finnhittson-creator/pogostick/pogostick/pogostick.kicad_sch

## KiCad design pogostick/pogostick.kicad_sch (2026-09-18)

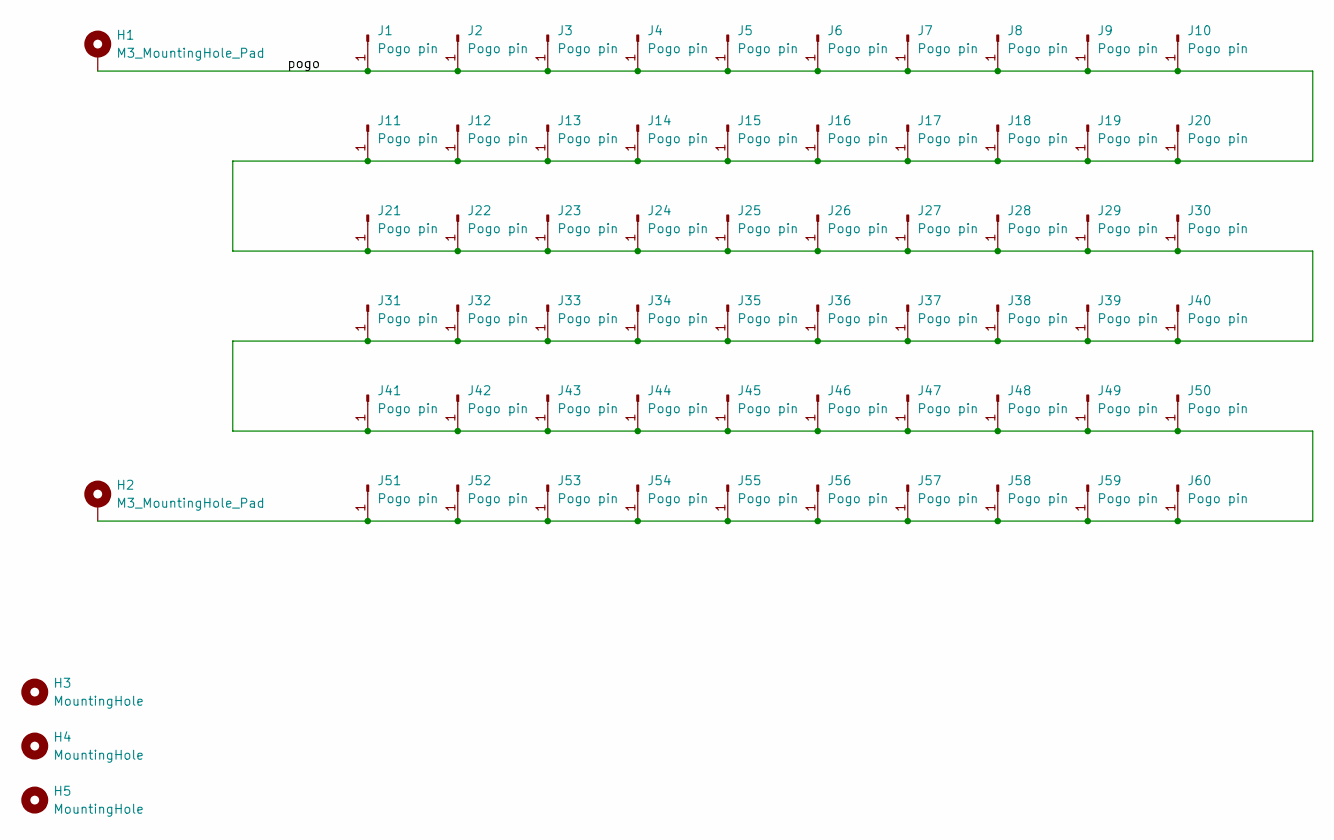
[picture p8: schematic pogostick.kicad_sch]

Parts:
H1, H2: M3_MountingHole_Pad; MountingHole_3.2mm_M3_ISO7380_Pad_TopBottom
H3, H4, H5: MountingHole; MountingHole_3.2mm_M3_ISO7380_Pad_TopBottom
J1, J2, J3, J4, J5, J6, J7, J8, J9, J10, J11, J12, J13, J14, J15, J16, J17, J18, J19, J20, J21, J22, J23, J24, J25, J26, J27, J28, J29, J30, J31, J32, J33, J34, J35, J36, J37, J38, J39, J40, J41, J42, J43, J44, J45, J46, J47, J48, J49, J50, J51, J52, J53, J54, J55, J56, J57, J58, J59, J60: Pogo pin; PogoPin_Pad_D1.83mm

Connections:
pogo: H1.1, H2.1, J1.1, J2.1, J3.1, J4.1, J5.1, J6.1, J7.1, J8.1, J9.1, J10.1, J11.1, J12.1, J13.1, J14.1, J15.1, J16.1, J17.1, J18.1, J19.1, J20.1, J21.1, J22.1, J23.1, J24.1, J25.1, J26.1, J27.1, J28.1, J29.1, J30.1, J31.1, J32.1, J33.1, J34.1, J35.1, J36.1, J37.1, J38.1, J39.1, J40.1, J41.1, J42.1, J43.1, J44.1, J45.1, J46.1, J47.1, J48.1, J49.1, J50.1, J51.1, J52.1, J53.1, J54.1, J55.1, J56.1, J57.1, J58.1, J59.1, J60.1
